salazarr-js/pocket-groovebox/docs/hardware/modules/st7789.md

# ST7789 1.9" 170×320 IPS LCD (generic)

Color SPI display for the UI — menus, BPM, presets, waveforms.

| | |
| --- | --- |
| **Role** | Display (SPI TFT) |
| **Driver chip** | Sitronix ST7789V |
| **Variant on hand** | Generic 1.9" IPS module, no brand (matches the lcdwiki MSP1901 design) |
| **Resolution** | 170 × 320 |
| **Panel** | IPS, 65K colors (RGB565; controller supports up to 262K) |
| **Interface** | 4-wire SPI (write-only — no MISO) |
| **Operating voltage** | 3.3 V |
| **Active area** | 22.695 × 42.72 mm |
| **PCB size** | 29 × 62 mm (≈13 g) |
| **Temp range** | −10 to 60 °C (operating) |
| **Source** | — |
| **Price** | — |
| **Quantity** | 1 |

## Datasheets & references

- Matching module docs (same specs/pinout/dimensions, sample code for STM32/C51/MSP430): [lcdwiki — 1.9inch IPS Module (MSP1901)](https://www.lcdwiki.com/1.9inch_IPS_Module)
- ST7789 controller — pinout, init, and sample code from any 170×320 ST7789 source apply.
- Compatible reference (same controller/resolution): [Waveshare 1.9inch LCD Module wiki](https://www.waveshare.com/wiki/1.9inch_LCD_Module)
- Arduino walkthrough (TFT_eSPI): [done.land — 1.9" 170×320 ST7789](https://done.land/components/humaninterface/display/tft/st7789/1.9inch320x240/)
- Same controller/resolution, good libraries + learn guide (different, fancier breakout — adds microSD, level shifting): [Adafruit 1.9" 320×170 ST7789](https://www.adafruit.com/product/5394)

## Photos

| Top | Bottom |
| --- | --- |
| ST7789 1.9in top | ST7789 1.9in bottom |

> Images: [lcdwiki — 1.9inch IPS Module](https://www.lcdwiki.com/1.9inch_IPS_Module)

## Module pins

Labels vary by board; common 8-pin generic layout:

| Pin | Function |
| --- | --- |
| GND | Ground |
| VCC | 3.3 V supply |
| SCL / CLK | SPI clock (SCLK) |
| SDA / DIN | SPI data in (MOSI) |
| RES / RST | Reset (active low) |
| DC | Data / command select |
| CS | Chip select (active low) |
| BLK / BL | Backlight (PWM-able for brightness) |

## Notes & gotchas

- **Write-only SPI** — the host never reads back, so there's no MISO line.
- **170×320 offset = 35.** The ST7789 controller RAM is 240×320; the 170-wide panel sits offset by (240−170)/2 = **35 columns**. Wrong/zero offset → image shifted or wrapped. **TFT_eSPI** applies it automatically when you set `TFT_WIDTH 170` / `TFT_HEIGHT 320` with the ST7789 driver; **LovyanGFX**: set `offset_x = 35`. Also supported by **Arduino_GFX** and the **Adafruit ST7789** library.
- **Colors may need inversion.** ST7789 IPS panels usually want display inversion ON — if colors look negative/washed, toggle it (`tft.invertDisplay(true/false)`).
- Active area 22.695 × 42.72 mm on a 29 × 62 mm PCB — note these for the handheld enclosure layout.
- **Many brands sell this panel** (lcdwiki/MSP1901 matches this board; Waveshare, Adafruit use the same ST7789 panel on a *different* PCB). Code is portable, but **pin order/labels differ between brands** — wire by *this* board's silkscreen, not another brand's.
- Connections to the ESP32-S3 → see [../wiring.md](../wiring.md#connections).
