salazarr-js/pocket-groovebox/docs/brief.md

# Pocket Groovebox — Project Brief

> 🎹 A modern DIY pocket groovebox. Just for fun.

## Origin

The project started after receiving a **Stylophone Beat** as a gift from a friend. It sparked interest in portable music devices, standalone instruments, tactile interfaces, embedded systems, and realtime interaction.

> Small playful devices can inspire surprisingly deep creative experiences.

## Vision

Build a single portable, playful music instrument — a modern, reimagined Stylophone in the form of a standalone pocket groovebox — refined over a few iterations.

The goal is instant fun, tactile interaction, playful experimentation, minimal interfaces, and portable creativity.

## Inspirations

No single device is the blueprint. Each one below contributes a piece — the spirit, the play style, the form factor, or a lesson about restraint — and together they point at what Pocket Groovebox should feel like.

| | Source | Role | Takeaway |
| --- | --- | --- | --- |
|  | [Stylophone Beat](https://stylophone.com/product/stylophone-beat) | Foundational | The instrument that started it all — the thing to reimagine |
|  | [Hichord](https://hichord.shop/) | Primary | Core inspiration for the instrument concept and play style |
|  | [Aftersound LOOPA](https://aftersound.tech/) | Primary | Battery-powered "musical multi-tool" — poly synth + tape recorder + step sequencer + live looper in one pocket device; closest match to this project's scope |
|  | [Teenage Engineering OP-1](https://teenage.engineering/products/op-1) | Primary | Personality and interaction design beat feature count |
|  | [minichord](https://minichord.com/) | Primary | Open-source pocket chord instrument (open PCB, BOM, 3D enclosure + firmware) — closest DIY reference for a chord-based build; see also `sketches/16-omnichord` |
|  | [CHOMPI](https://www.chompiclub.com/) | Primary | Playful all-in-one sampler/looper groovebox — character-driven design, tactile keys + hands-on sampling, joyful "instant fun" feel in a pocketable box |
|  | [Steam Deck](https://www.steamdeck.com/) | Form factor | Handheld console look and feel — held in two hands, screen + controls |
|  | [Teenage Engineering Pocket Operator family](https://teenage.engineering/products/po) | Secondary | Pocket form factor, creative constraints, minimal UI |
|  | [Korg nanoKEY2](https://www.korg.com/us/products/computergear/nanokey2/) | Secondary | Compact one-octave mini-key keyboard |
|  | [M-Vave SMK25 Mini](https://www.m-vave.com/product?id=smk25-mini) | Secondary | Compact mini-key MIDI keyboard in a portable layout |
|  | [Korg Monotron family](https://www.korg.com/us/products/dj/monotron_duo/) | Secondary | Tiny analog synths — physical controls as part of the experience |
|  | [M-Vave FM-1](https://www.m-vave.com/product?id=fm-1) | Secondary | Battery-powered DX-7-style FM polysynth with built-in speaker, 27 keys, TFT screen, 16-step sequencer + arpeggiator — an all-in-one pocket synth in the same class |
| | [Roland TB-303](https://en.wikipedia.org/wiki/Roland_TB-303) | Secondary (sound) | The acid-bassline machine — squelchy resonant lowpass + slide/accent step sequencer. Origin of the whole "303-style" sound; reference for an acid-bass engine, and a case study in how a synth's *character* can define a genre |
| | [Donner Essential B1](https://us.donnermusic.com/products/donner-synthesizer-and-sequencer-analog-bass-b1) | Secondary (sound) | Modern, affordable **303-style** acid-bass synth + sequencer (Red Dot 2022) — silicone keys with colour-changing backlight; a current pocket-sized take on the TB-303 formula |
| | [Roland TR-606](https://en.wikipedia.org/wiki/Roland_TR-606) | Secondary (drums) | *Drumatix* — the analog drum machine companion to the TB-303 in the classic acid setup. Reference for the synthesized-drum voices + step sequencer (see [research/drums.md](research/drums.md), already "TR-606-style") |
| | Panasonic R1088 | Secondary | |
| | Roland P-6 | Secondary | |
| | [Casio SK-1](https://en.wikipedia.org/wiki/Casio_SK-1) | Secondary | |

> 🔬 **To research (later):** every inspiration source above deserves a proper deep-research report — pull the full product story, design decisions, feature set, community reception, and the specific lesson for Pocket Groovebox — so this table becomes a set of studied references rather than links. Not doing it now; just flagging it.

> 🔬 **To research (later):** why is *"303-style"* a genre of its own? What makes the TB-303's sound + sequencer so endlessly cloned (Donner B1, Behringer TD-3, Roland TB-03…), and what of it belongs in this synth's engine. Feeds the synthesis-system research (`docs/research/synthesis.md`).

### Videos

- [NES-SY2.0 Nintendo homage synth](https://www.youtube.com/watch?v=KWfsQgcx9cc) — Nintendo-inspired synthesizer build
- [Custom Isomorphic Keyboard Demo](https://youtu.be/9wTGm-IKtV0) — demo of a custom isomorphic keyboard
- [Custom Isomorphic Keyboard — Technical Breakdown](https://youtu.be/jn62QLrfST8) — technical breakdown of the build

## Product Concept

A **modern**, lightweight, battery-powered standalone synthesizer / sampler / loop station with a step sequencer, in a **handheld console form factor** (OP-1 × HiChord layout — screen and controls above, keyboard below), with a built-in speaker, display, and a 2-octave 24-key keyboard (C3–B4). Works without a computer or internet.

> Concept renders exploring form factor and layout: see [design.md](design.md).

## Design Principles

1. **Instant fun** — playable within seconds of power-on; every control does something audible immediately.
2. **Playful minimalism** — few controls and shallow menus (no deeper than two levels); add interaction depth, not button count.
3. **Standalone first, optional companion** — the device works on its own, with no computer or internet. Optional companion software (web or native) could improve the experience later — e.g. a visuals editor, sound packs, or a pattern editor — but it must never be required for play.
4. **Open, DIY hardware** — an open-source hardware project, not a product. Built from accessible, maker-friendly dev modules and community tools, and from techniques anyone can try at home: repurposed toy instruments, 3D-printed parts, laser-cut or CNC acrylic, robotics kits. Favor off-the-shelf and reusable over custom and specialized.

## Non-goals

This is **not** a DAW, a workstation, or a feature-heavy synth — and not a product line. No deep menus, no massive sample libraries, no chasing feature count. The constraints are the point.

## Success signals

- I reach for it instead of my phone when I have a spare minute.
- It makes sound within seconds of power-on, with no setup.
- A complete idea — a loop with a melody — comes together in one sitting, no manual needed.
